M4ngu/Sweet-Sixteen/20191105_181811.jpg

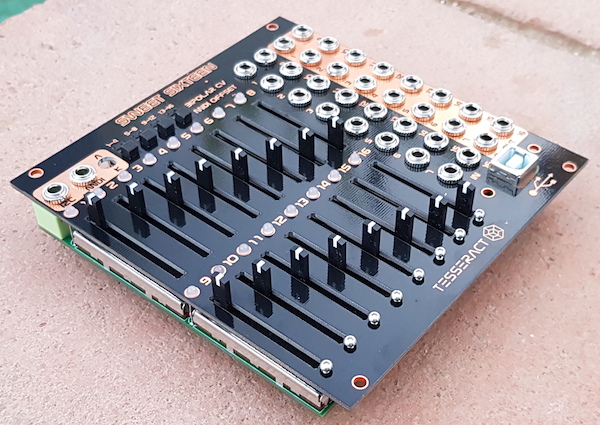
20191105_181811.jpg
